fdufnews/macropad/doc/IMG_20240220_082146.jpg

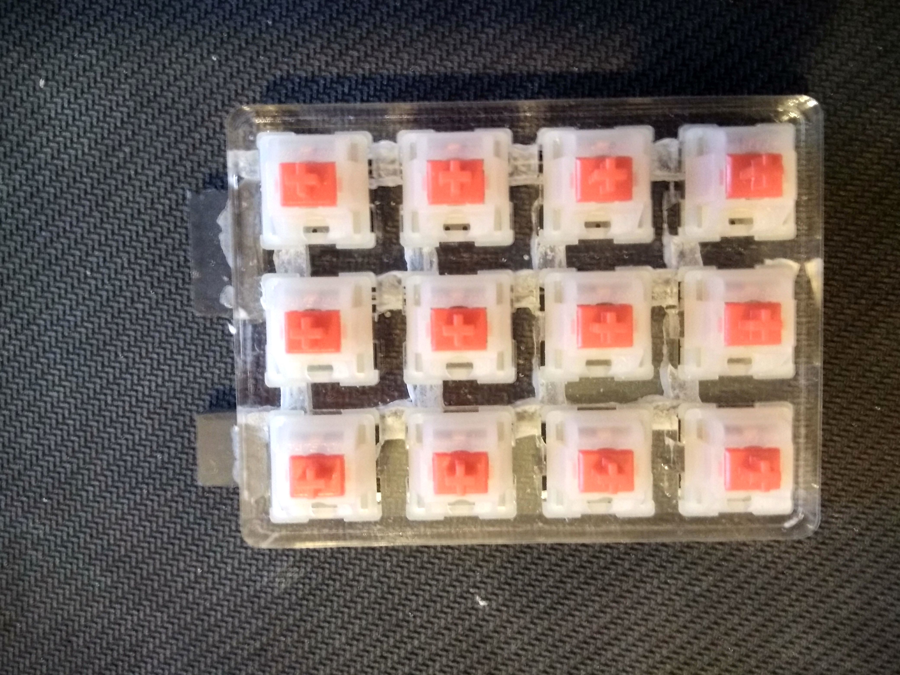
doc/IMG_20240220_082146.jpg
