fdufnews/macropad/doc/IMG_20240220_082203.jpg

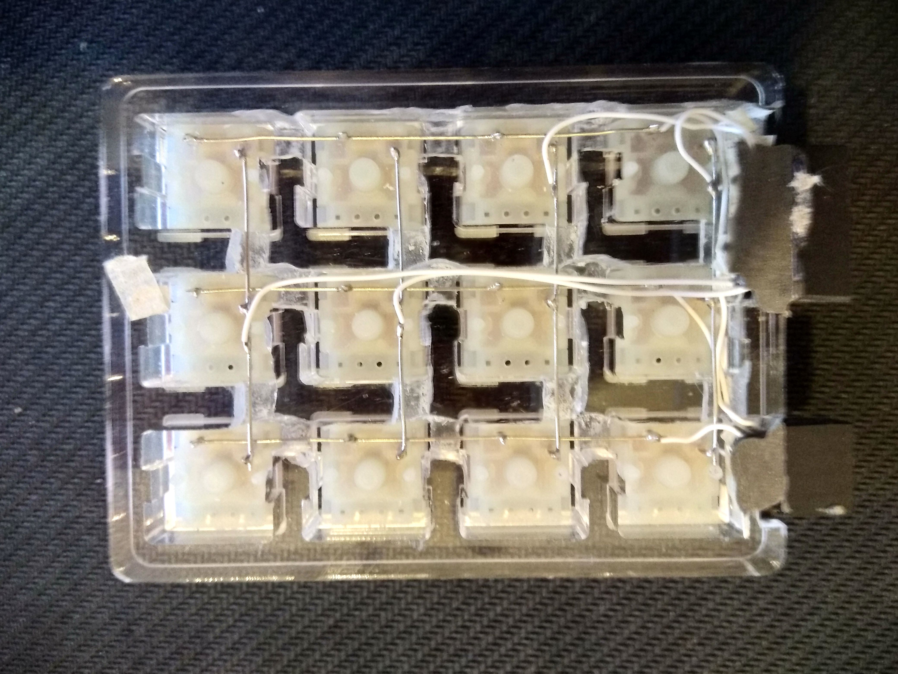
doc/IMG_20240220_082203.jpg
