fdufnews/macropad/doc/IMG_20240220_082411.jpg

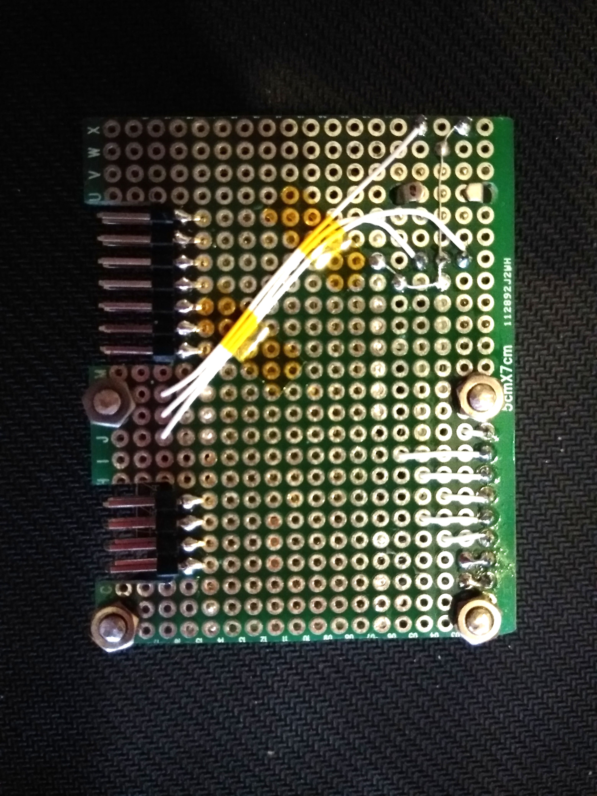
doc/IMG_20240220_082411.jpg
