fdufnews/macropad/doc/IMG_20240220_083248.jpg

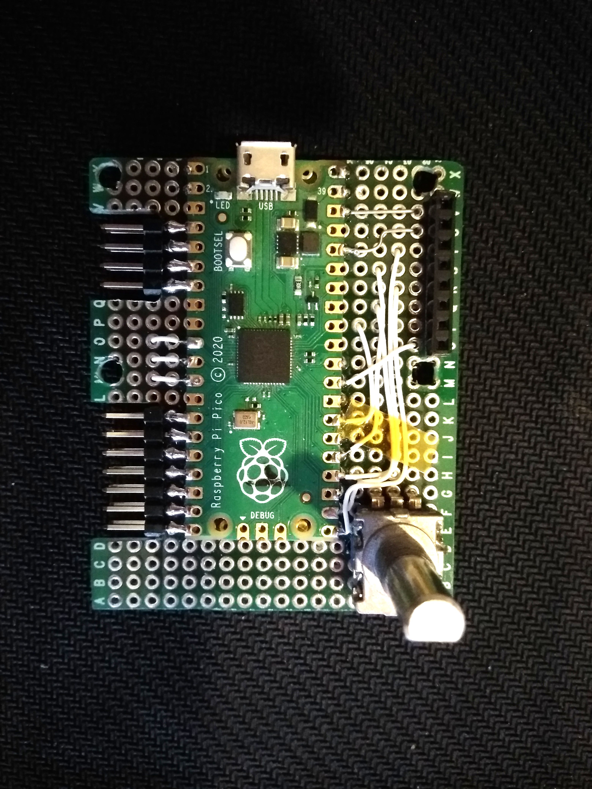
doc/IMG_20240220_083248.jpg
