fdufnews/macropad/doc/IMG_20240220_083311.jpg

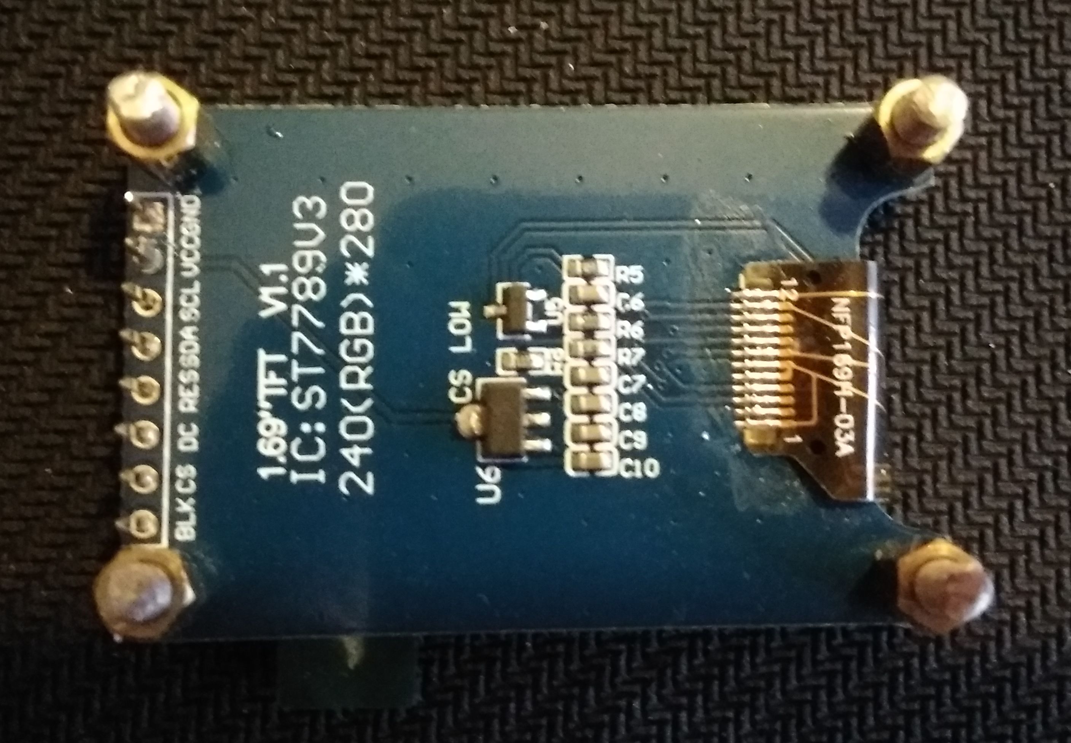
doc/IMG_20240220_083311.jpg
