fdufnews/macropad/doc/IMG_20240220_083927.jpg

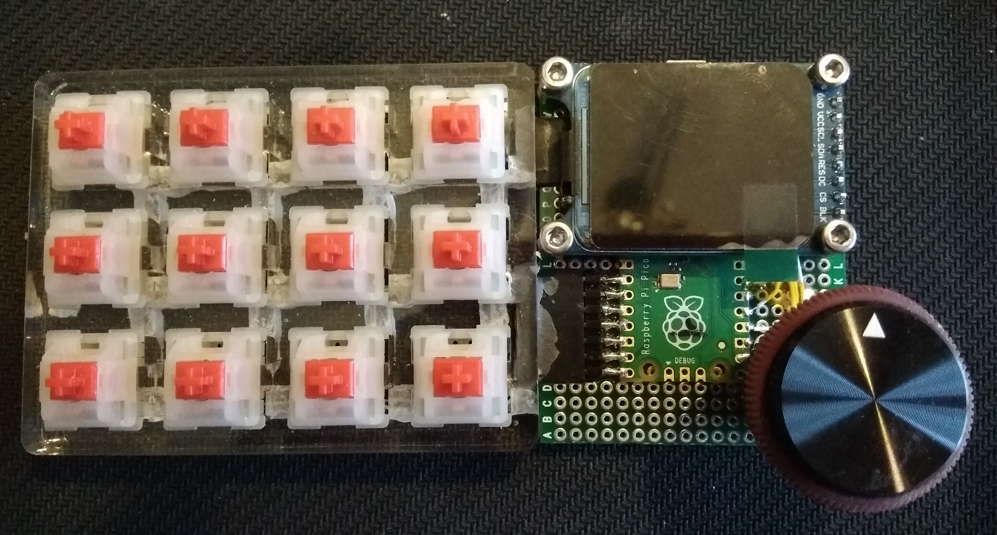
doc/IMG_20240220_083927.jpg
