fdufnews/macropad/hardware/MacroPad.kicad_sch

## KiCad design hardware/MacroPad.kicad_sch (2024-02-26)

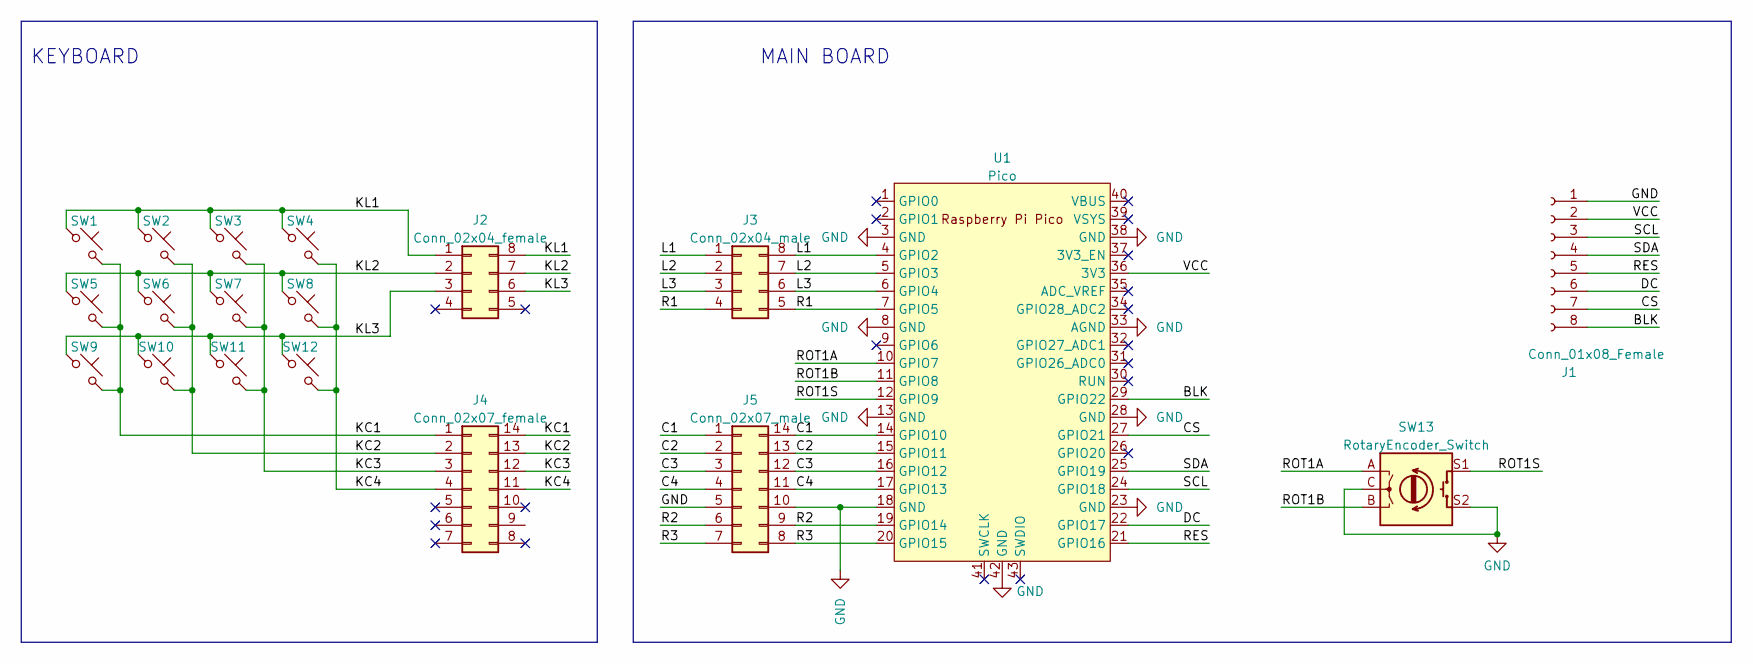
[picture p9: schematic MacroPad.kicad_sch]

Parts:
J1: Conn_01x08_Female
J2: Conn_02x04_female
J3: Conn_02x04_male
J4: Conn_02x07_female
J5: Conn_02x07_male
SW1, SW2, SW3, SW4, SW5, SW6, SW7, SW8, SW9, SW10, SW11, SW12: SW_Push_45deg
SW13: RotaryEncoder_Switch
U1: Pico; RPi_Pico_SMD_TH

Connections:
BLK: J1.8, U1.29 (GPIO22)
C1: J5.1, J5.14, U1.14 (GPIO10)
C2: J5.2, J5.13, U1.15 (GPIO11)
C3: J5.3, J5.12, U1.16 (GPIO12)
C4: J5.4, J5.11, U1.17 (GPIO13)
CS: J1.7, U1.27 (GPIO21)
DC: J1.6, U1.22 (GPIO17)
GND: J1.1, J5.5, J5.10, SW13.C, SW13.S2, U1.3 (GND), U1.8 (GND), U1.13 (GND), U1.18 (GND), U1.23 (GND), U1.28 (GND), U1.33 (AGND), U1.38 (GND), U1.42 (GND)
KC1: J4.1, J4.14, SW1.2, SW5.2, SW9.2
KC2: J4.2, J4.13, SW2.2, SW6.2, SW10.2
KC3: J4.3, J4.12, SW3.2, SW7.2, SW11.2
KC4: J4.4, J4.11, SW4.2, SW8.2, SW12.2
KL1: J2.1, J2.8, SW1.1, SW2.1, SW3.1, SW4.1
KL2: J2.2, J2.7, SW5.1, SW6.1, SW7.1, SW8.1
KL3: J2.3, J2.6, SW9.1, SW10.1, SW11.1, SW12.1
L1: J3.1, J3.8, U1.4 (GPIO2)
L2: J3.2, J3.7, U1.5 (GPIO3)
L3: J3.3, J3.6, U1.6 (GPIO4)
R1: J3.4, J3.5, U1.7 (GPIO5)
R2: J5.6, J5.9, U1.19 (GPIO14)
R3: J5.7, J5.8, U1.20 (GPIO15)
RES: J1.5, U1.21 (GPIO16)
ROT1A: SW13.A, U1.10 (GPIO7)
ROT1B: SW13.B, U1.11 (GPIO8)
ROT1S: SW13.S1, U1.12 (GPIO9)
SCL: J1.3, U1.24 (GPIO18)
SDA: J1.4, U1.25 (GPIO19)
VCC: J1.2, U1.36 (3V3)

Notes on the sheet:
KEYBOARD
MAIN BOARD
